alexeysirenko/antenna_arrays/dipoles/446mhz/плече_диполя.jpg

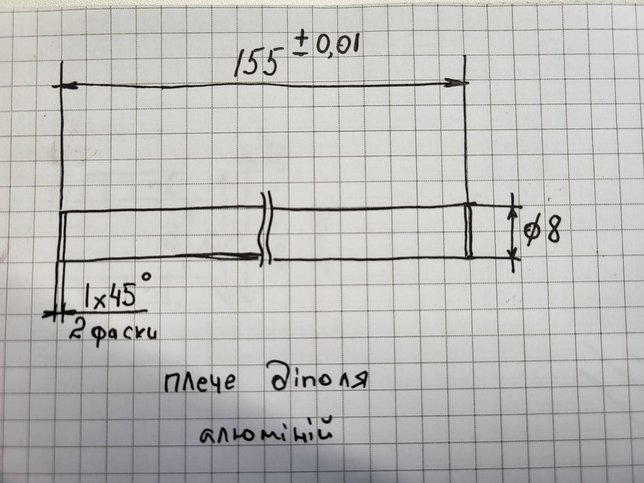
dipoles/446mhz/плече_диполя.jpg
