alexeysirenko/antenna_arrays/linear_array/img/img3.jpg

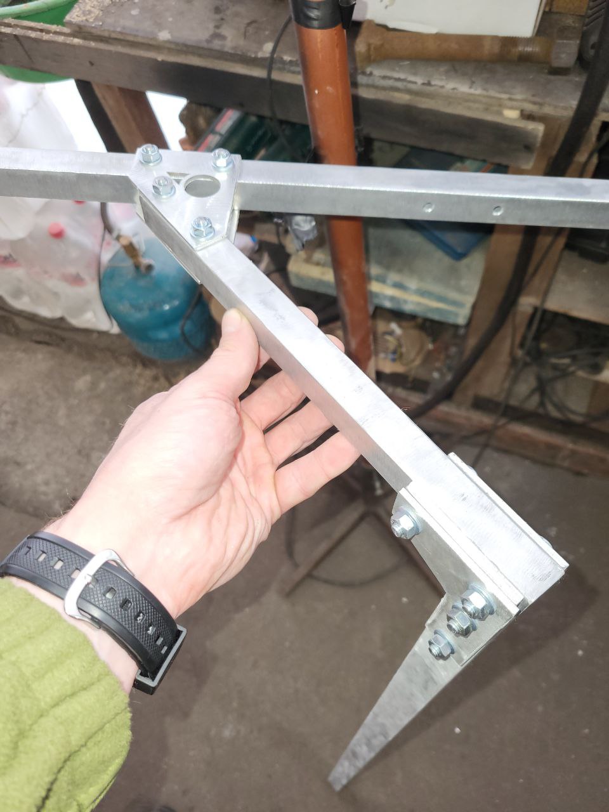
linear_array/img/img3.jpg
