alexeysirenko/antenna_arrays/linear_array/виніс.jpg

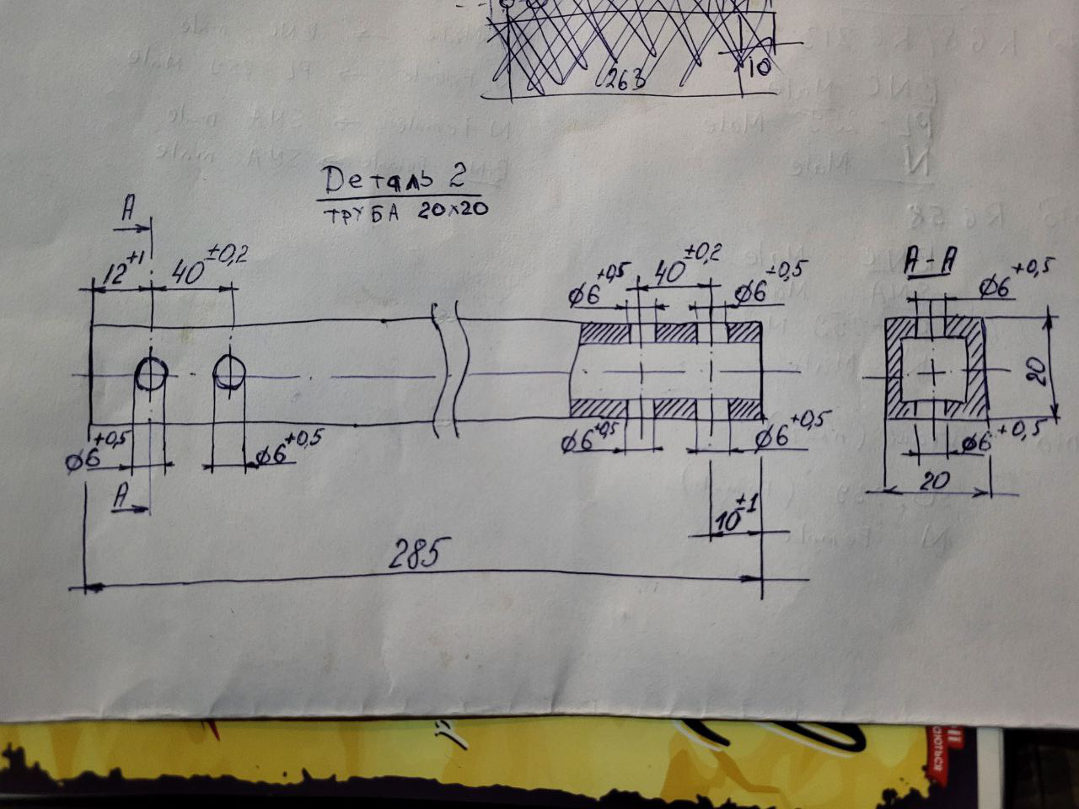
linear_array/виніс.jpg
