alexeysirenko/antenna_arrays/linear_array/мачта.jpg

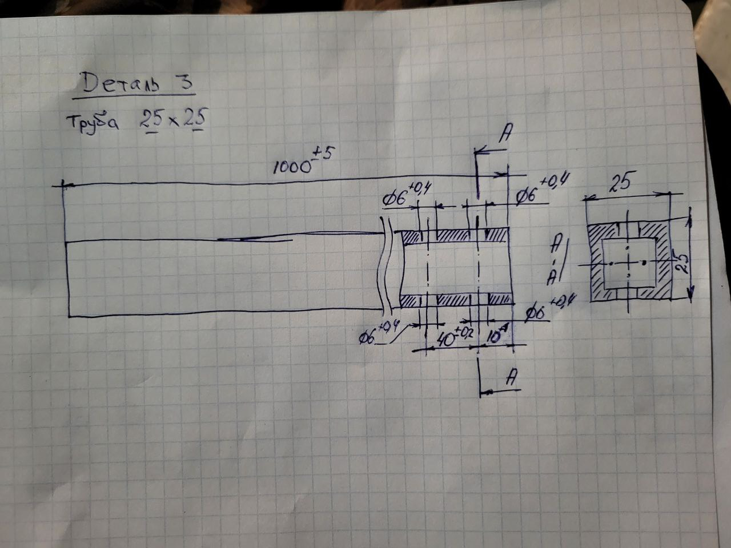
linear_array/мачта.jpg
