alexeysirenko/antenna_arrays/linear_array/траверса.jpg

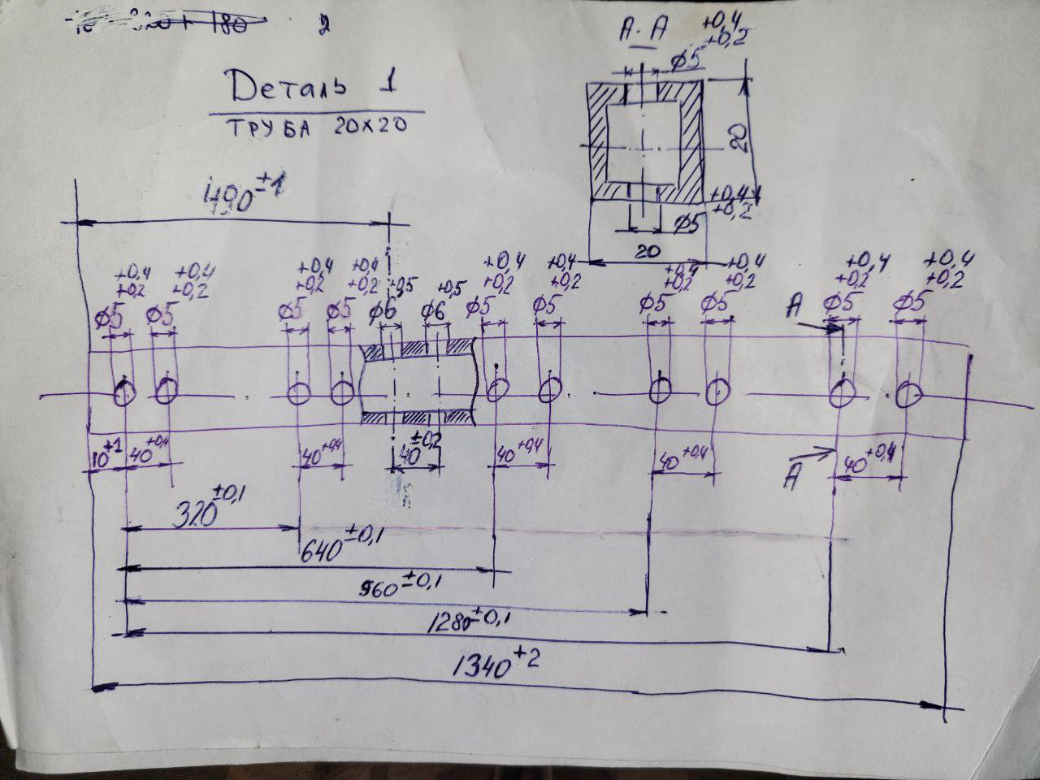
linear_array/траверса.jpg
